fanf2/kbd/hhkbeeb/owl/bbc-owl-256x256.png

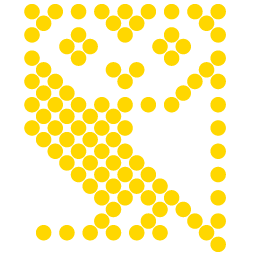
hhkbeeb/owl/bbc-owl-256x256.png
