fanf2/kbd/hhkbeeb/photos/2021-07-29-hs60-d-switches.jpg

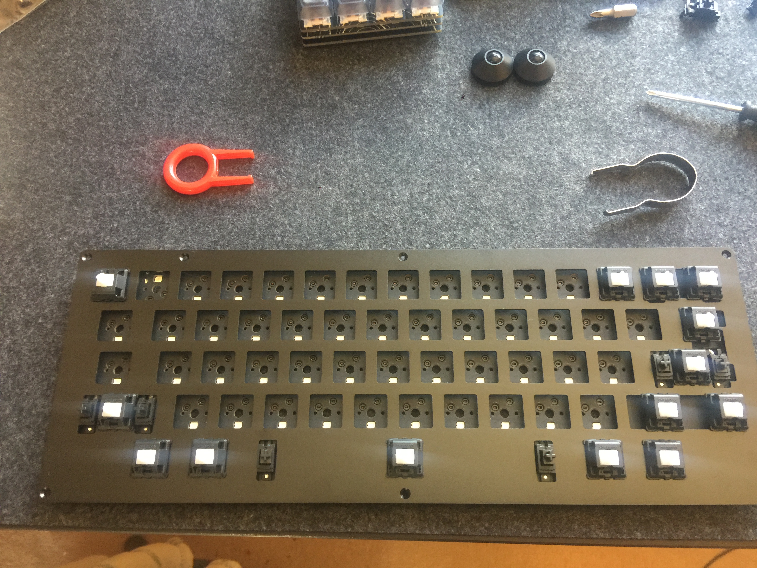
hhkbeeb/photos/2021-07-29-hs60-d-switches.jpg
