fanf2/kbd/hhkbeeb/photos/2021-07-29-hs60-i-caps.jpg

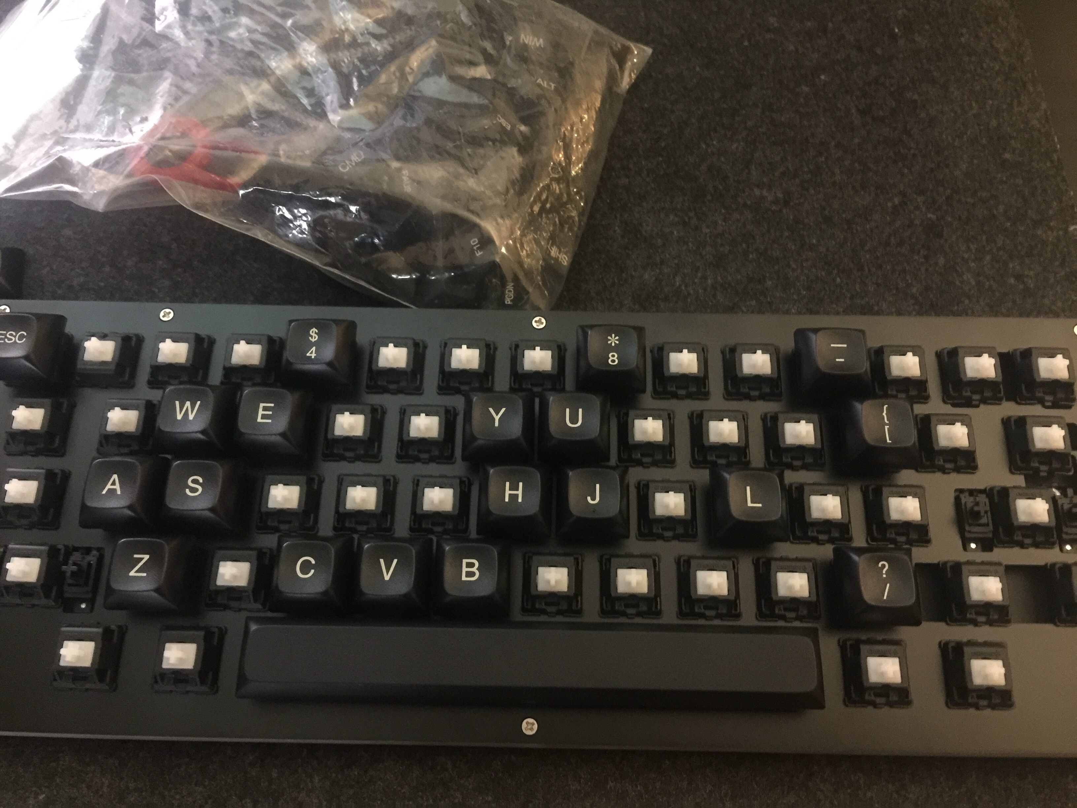
hhkbeeb/photos/2021-07-29-hs60-i-caps.jpg
