fanf2/kbd/hhkbeeb/photos/2021-07-29-hs60-k-glow.jpg

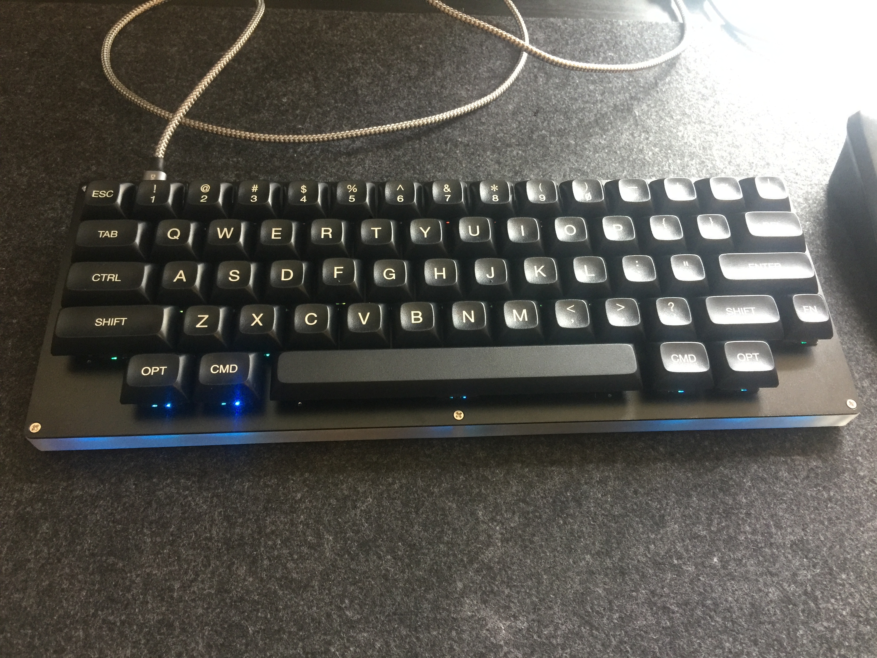
hhkbeeb/photos/2021-07-29-hs60-k-glow.jpg
