fanf2/kbd/hhkbeeb/photos/2021-08-20-screws-black.jpg

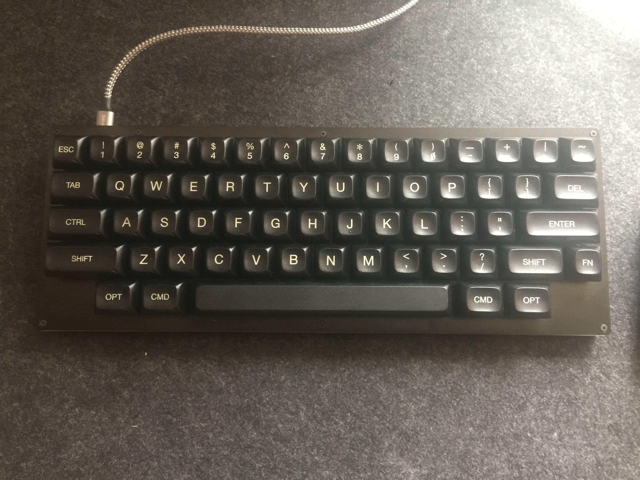
hhkbeeb/photos/2021-08-20-screws-black.jpg
