fanf2/kbd/hhkbeeb/photos/2021-08-26-a-keycaps.jpg

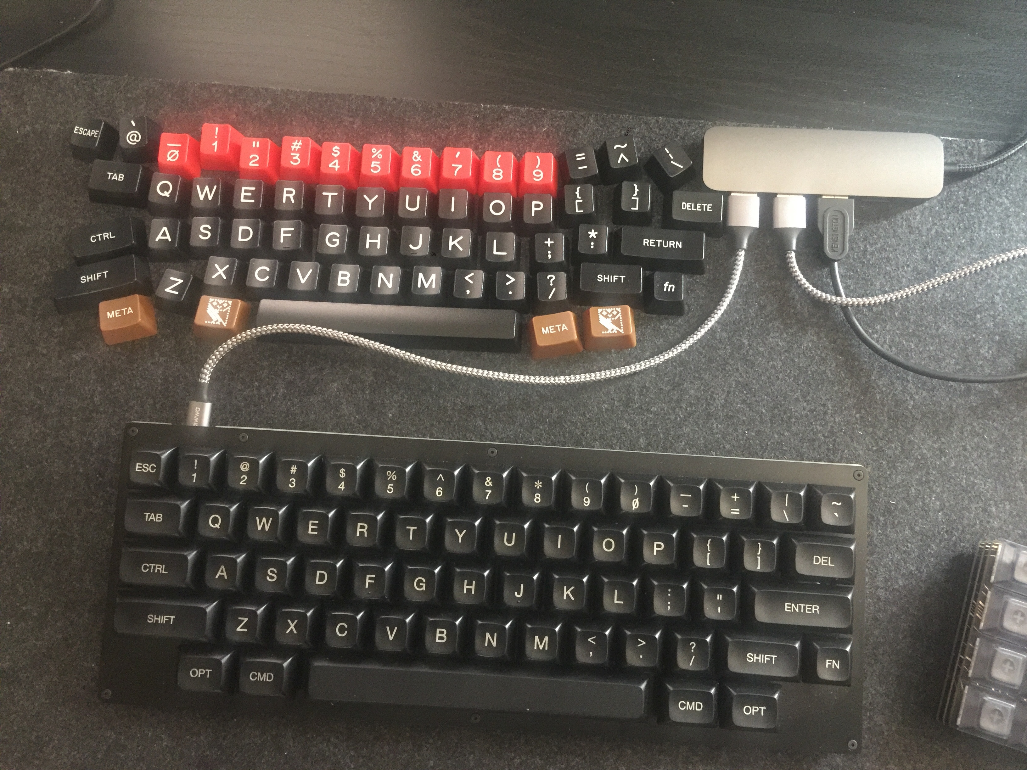
hhkbeeb/photos/2021-08-26-a-keycaps.jpg
