fanf2/kbd/hhkbeeb/photos/2021-08-26-b-mod-switches.jpg

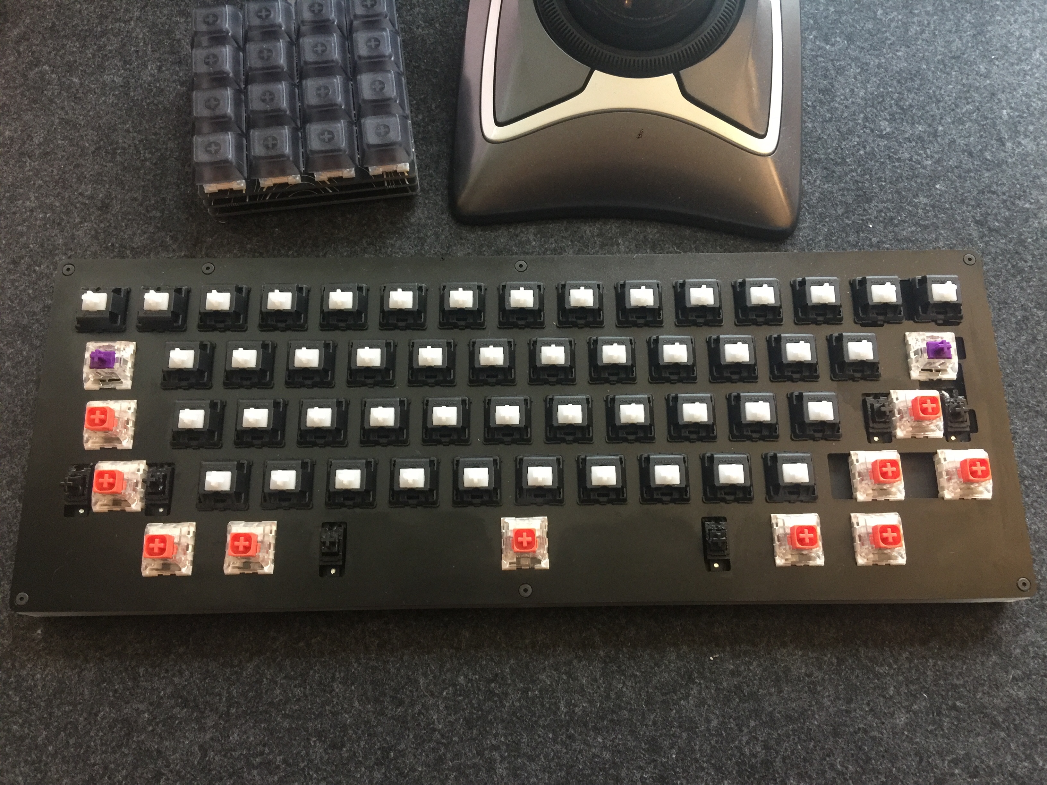
hhkbeeb/photos/2021-08-26-b-mod-switches.jpg
