fanf2/kbd/hhkbeeb/photos/2021-08-26-d-red-caps.jpg

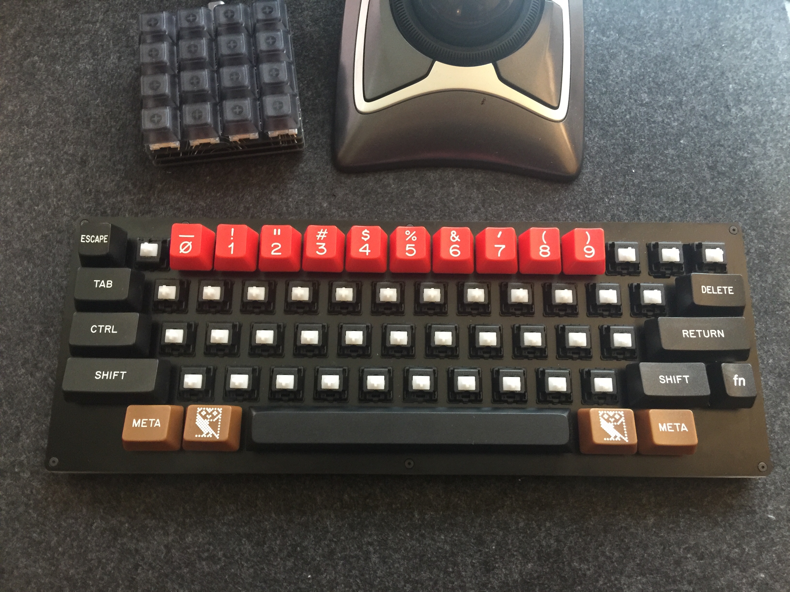
hhkbeeb/photos/2021-08-26-d-red-caps.jpg
