fanf2/kbd/hhkbeeb/photos/2021-08-26-e-bbc-hhkb.jpg

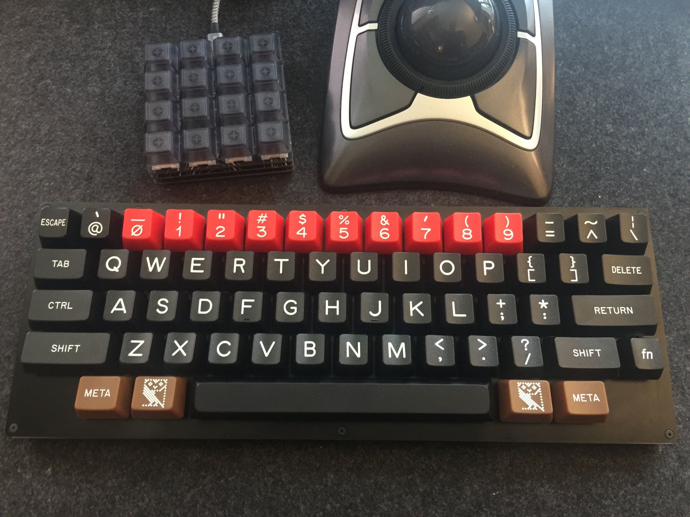
hhkbeeb/photos/2021-08-26-e-bbc-hhkb.jpg
