fanf2/kbd/hhkbeeb/photos/2021-08-26-g-owl.jpg

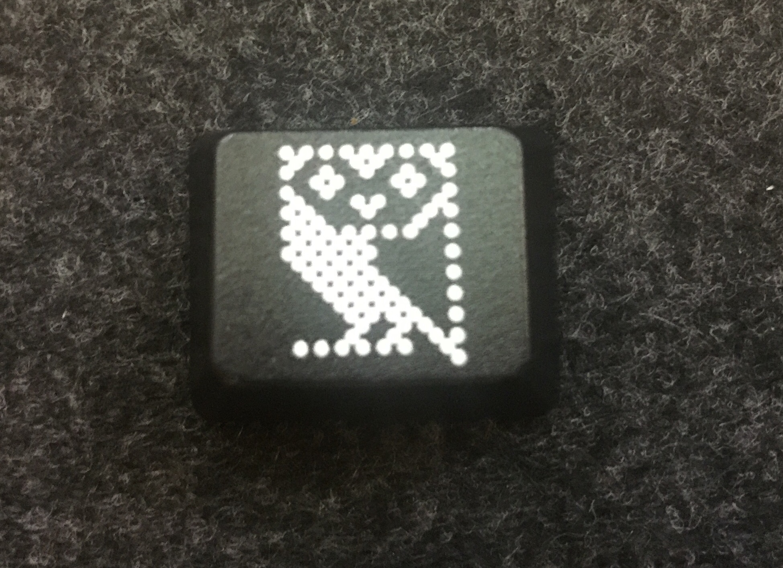
hhkbeeb/photos/2021-08-26-g-owl.jpg
