fanf2/kbd/hhkbeeb/photos/2021-08-26-h-space-cadet.jpg

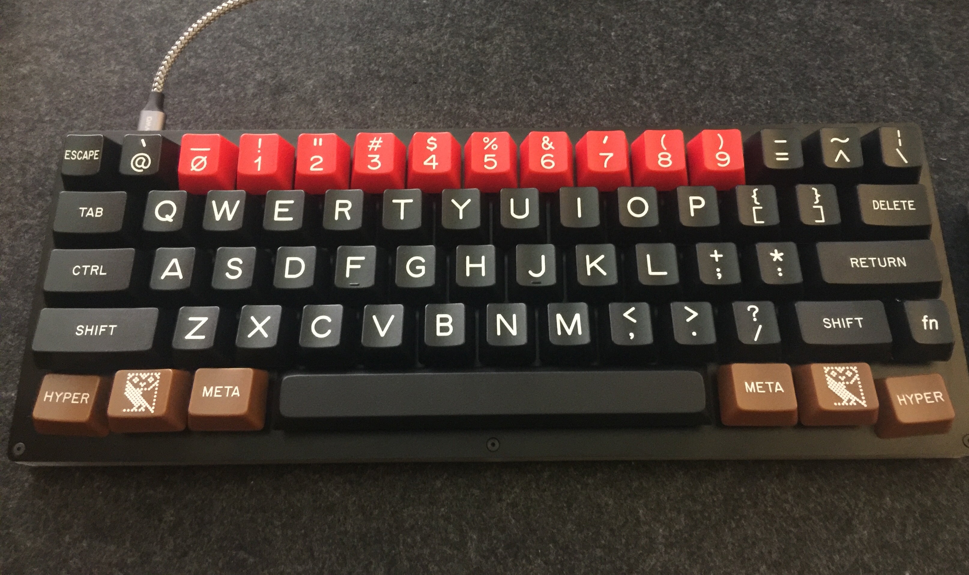
hhkbeeb/photos/2021-08-26-h-space-cadet.jpg
