fanf2/kbd/hhkbeeb/wasd/quarkwell-at.png

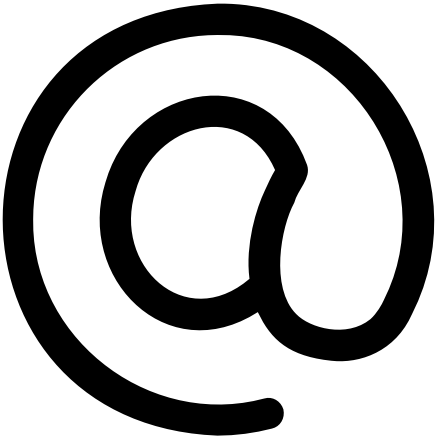
hhkbeeb/wasd/quarkwell-at.png
