fanf2/kbd/iobird-1/iobird/iobird.kicad_sch

## KiCad design iobird-1/iobird/iobird.kicad_sch (2023-12-12)

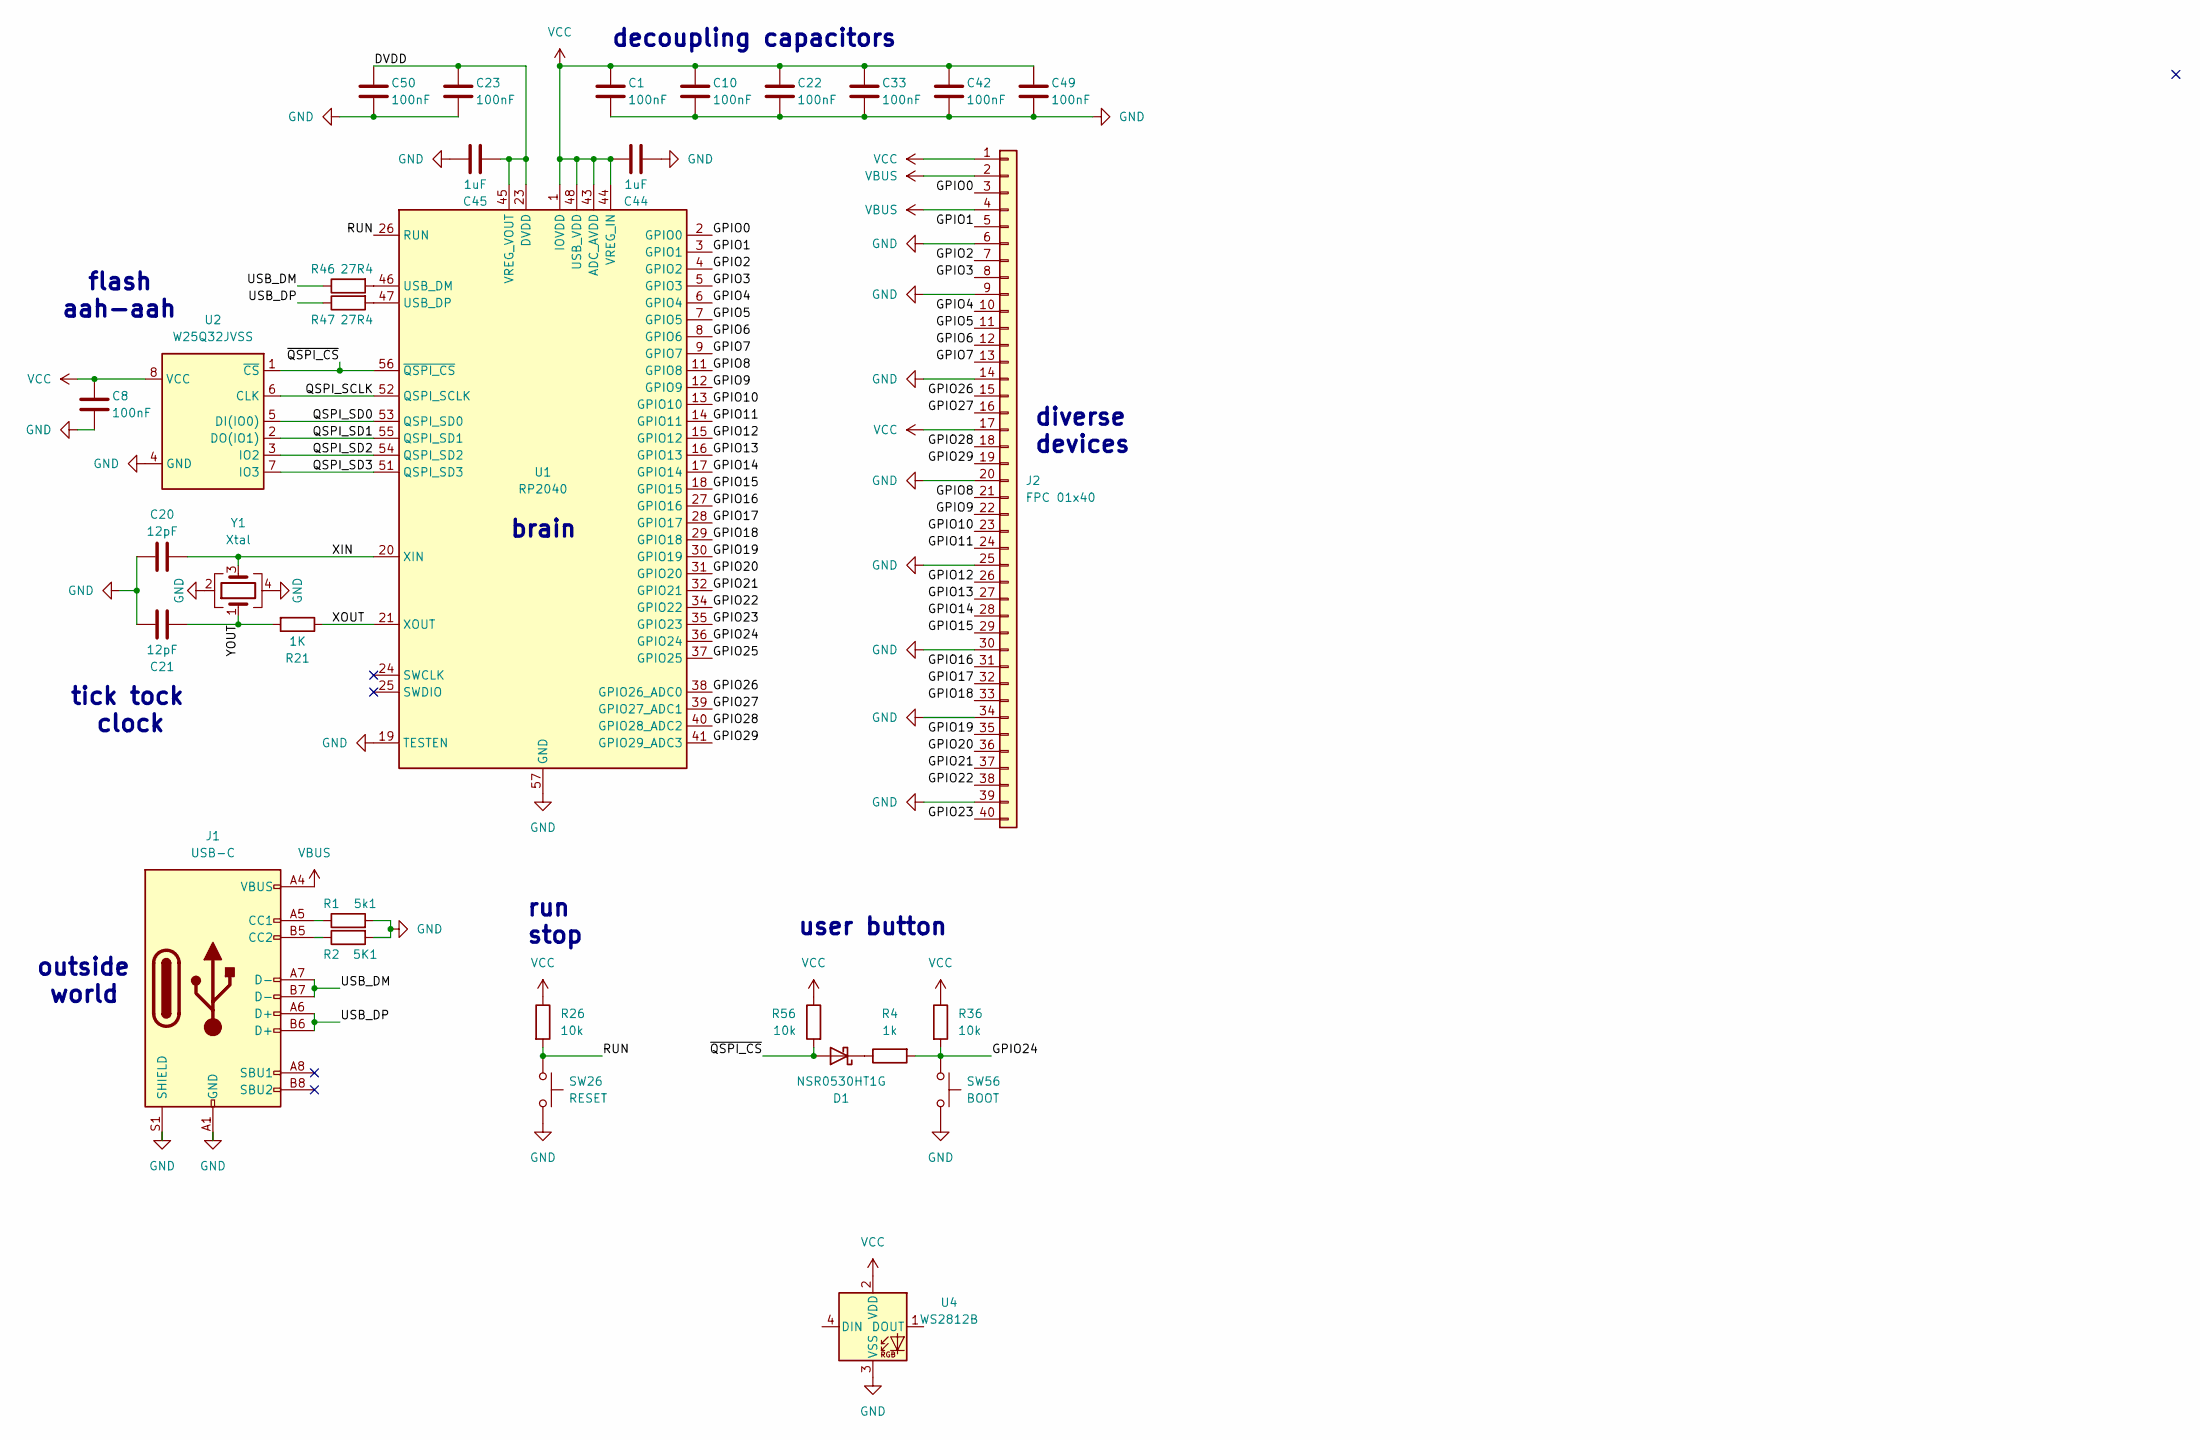
[picture p28: schematic iobird.kicad_sch]

Parts:
C1, C8, C10, C22, C23, C33, C42, C49, C50: 100nF
C20, C21: 12pF; C_0402_1005Metric
C44, C45: 1uF
D1: NSR0530HT1G
J1: USB-C
J2: FPC 01x40
R1: 5k1; R_0402_1005Metric
R2: 5K1; R_0402_1005Metric
R4: 1k
R21: 1K; R_0402_1005Metric
R26, R36, R56: 10k
R46, R47: 27R4
SW26: RESET
SW56: BOOT
U1: RP2040; QFN-56-1EP_7x7mm_P0.4mm_EP3.2x3.2mm
U2: W25Q32JVSS; SOIC-8_5.23x5.23mm_P1.27mm
U4: WS2812B; LED_WS2812B_PLCC4_5.0x5.0mm_P3.2mm
Y1: Xtal; Crystal_SMD_2520-4Pin_2.5x2.0mm

Connections:
DVDD: C23.2, C45.2, C50.2, U1.23 (DVDD), U1.45 (VREG_VOUT), U1.50 (DVDD)
GND: C1.1, C8.1, C10.1, C20.1, C21.1, C22.1, C23.1, C33.1, C42.1, C44.2, C45.1, C49.1, C50.1, J1.A1 (GND), J1.A12 (GND), J1.B1 (GND), J1.B12 (GND), J1.S1 (SHIELD), J2.6, J2.9, J2.14, J2.20, J2.25, J2.30, J2.34, J2.39, R1.2, R2.2, SW26.2, SW56.2, U1.19 (TESTEN), U1.57 (GND), U2.4 (GND), U4.3 (VSS), Y1.2, Y1.4
GPIO0: J2.3, U1.2 (GPIO0)
GPIO1: J2.5, U1.3 (GPIO1)
GPIO2: J2.7, U1.4 (GPIO2)
GPIO3: J2.8, U1.5 (GPIO3)
GPIO4: J2.10, U1.6 (GPIO4)
GPIO5: J2.11, U1.7 (GPIO5)
GPIO6: J2.12, U1.8 (GPIO6)
GPIO7: J2.13, U1.9 (GPIO7)
GPIO8: J2.21, U1.11 (GPIO8)
GPIO9: J2.22, U1.12 (GPIO9)
GPIO10: J2.23, U1.13 (GPIO10)
GPIO11: J2.24, U1.14 (GPIO11)
GPIO12: J2.26, U1.15 (GPIO12)
GPIO13: J2.27, U1.16 (GPIO13)
GPIO14: J2.28, U1.17 (GPIO14)
GPIO15: J2.29, U1.18 (GPIO15)
GPIO16: J2.31, U1.27 (GPIO16)
GPIO17: J2.32, U1.28 (GPIO17)
GPIO18: J2.33, U1.29 (GPIO18)
GPIO19: J2.35, U1.30 (GPIO19)
GPIO20: J2.36, U1.31 (GPIO20)
GPIO21: J2.37, U1.32 (GPIO21)
GPIO22: J2.38, U1.34 (GPIO22)
GPIO23: J2.40, U1.35 (GPIO23)
GPIO24: R4.2, R36.2, SW56.1, U1.36 (GPIO24)
GPIO25: U1.37 (GPIO25)
GPIO26: J2.15, U1.38 (GPIO26_ADC0)
GPIO27: J2.16, U1.39 (GPIO27_ADC1)
GPIO28: J2.18, U1.40 (GPIO28_ADC2)
GPIO29: J2.19, U1.41 (GPIO29_ADC3)
unnamed: D1.1 (K), R4.1
unnamed: J1.A5 (CC1), R1.1
unnamed: J1.B5 (CC2), R2.1
unnamed: R46.2, U1.46 (USB_DM)
unnamed: R47.2, U1.47 (USB_DP)
QSPI_SCLK: U1.52 (QSPI_SCLK), U2.6 (CLK)
QSPI_SD0: U1.53 (QSPI_SD0), U2.5 (DI(IO0))
QSPI_SD1: U1.55 (QSPI_SD1), U2.2 (DO(IO1))
QSPI_SD2: U1.54 (QSPI_SD2), U2.3 (IO2)
QSPI_SD3: U1.51 (QSPI_SD3), U2.7 (IO3)
RUN: R26.2, SW26.1, U1.26 (RUN)
USB_DM: J1.A7 (D-), J1.B7 (D-), R46.1
USB_DP: J1.A6 (D+), J1.B6 (D+), R47.1
VBUS: J1.A4 (VBUS), J1.A9 (VBUS), J1.B4 (VBUS), J1.B9 (VBUS), J2.2, J2.4
VCC: C1.2, C8.2, C10.2, C22.2, C33.2, C42.2, C44.1, C49.2, J2.1, J2.17, R26.1, R36.1, R56.1, U1.1 (IOVDD), U1.10 (IOVDD), U1.22 (IOVDD), U1.33 (IOVDD), U1.42 (IOVDD), U1.43 (ADC_AVDD), U1.44 (VREG_IN), U1.48 (USB_VDD), U1.49 (IOVDD), U2.8 (VCC), U4.2 (VDD)
XIN: C20.2, U1.20 (XIN), Y1.3
XOUT: R21.1, U1.21 (XOUT)
YOUT: C21.2, R21.2, Y1.1
~QSPI_CS: D1.2 (A), R56.2, U1.56 (~QSPI_CS), U2.1 (~CS)

Notes on the sheet:
brain
run stop
outside world
flash aah-aah
tick tock clock
diverse devices
decoupling capacitors
user button
